MCITBA/Lok_Prak_Rob/Bilder/Gesamtsystem_hinten.png

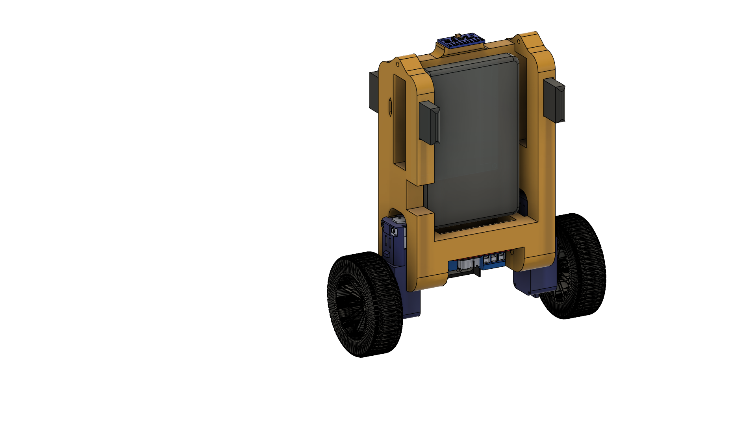
Bilder/Gesamtsystem_hinten.png
