MCITBA/Lok_Prak_Rob/iCloud Fotos/IMG_4470.PNG

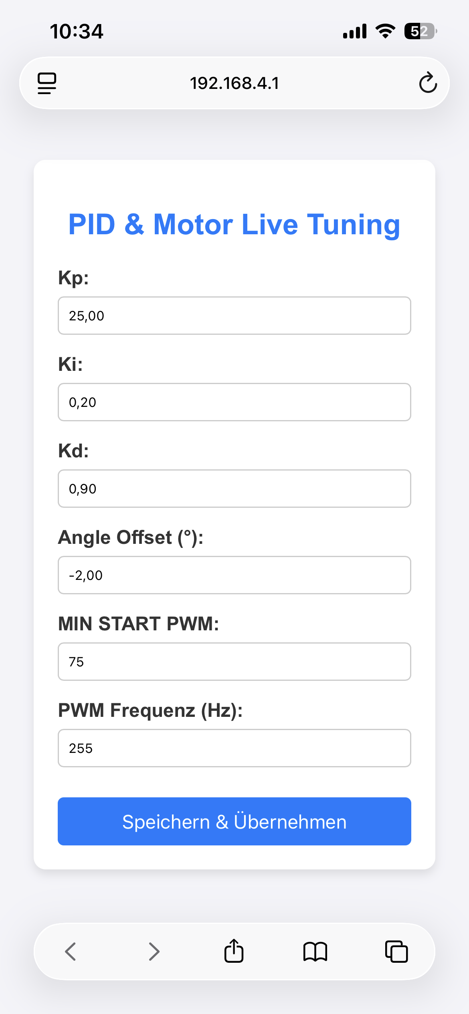
iCloud Fotos/IMG_4470.PNG
