MCITBA/Lok_Prak_Rob/iCloud Fotos/IMG_4471.PNG

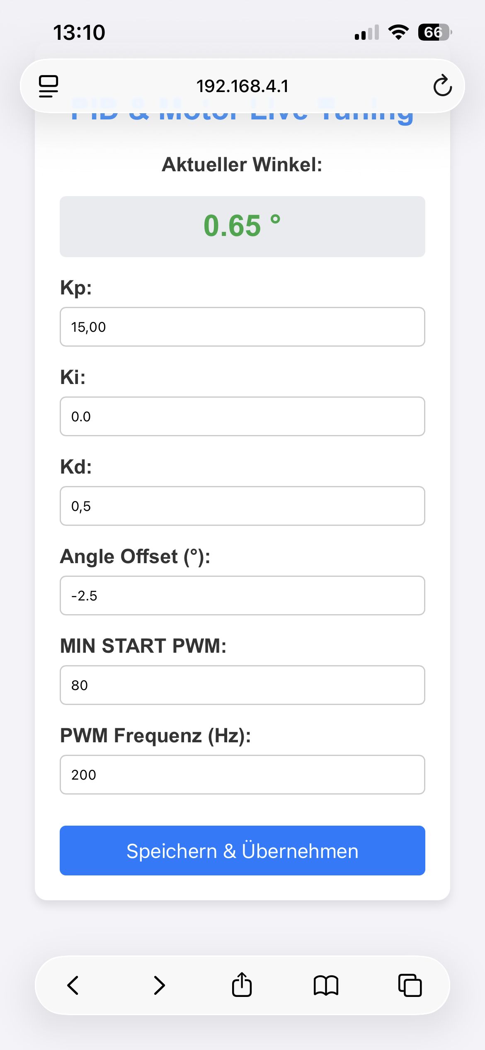
iCloud Fotos/IMG_4471.PNG
