MCITBA/Lok_Prak_Rob/iCloud Fotos/IMG_4481.JPEG

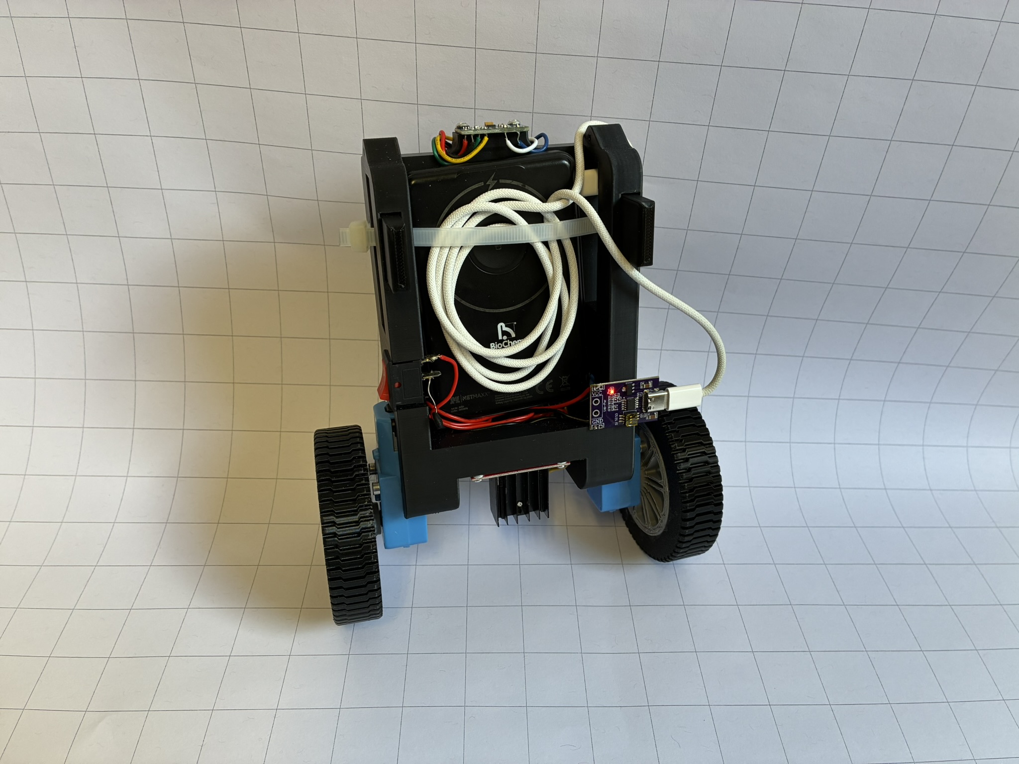
iCloud Fotos/IMG_4481.JPEG
