MCITBA/Lok_Prak_Rob/iCloud Fotos/IMG_4482.JPEG

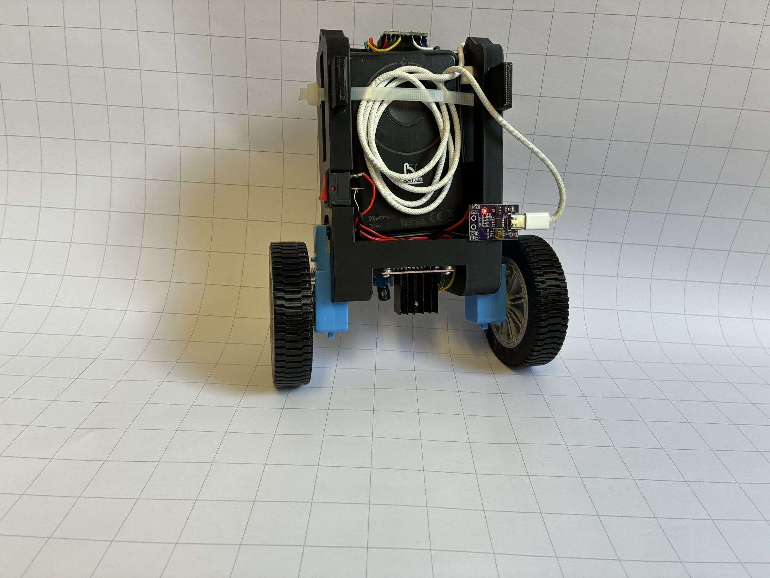
iCloud Fotos/IMG_4482.JPEG
