MCITBA/Lok_Prak_Rob/iCloud Fotos/IMG_4483.JPEG

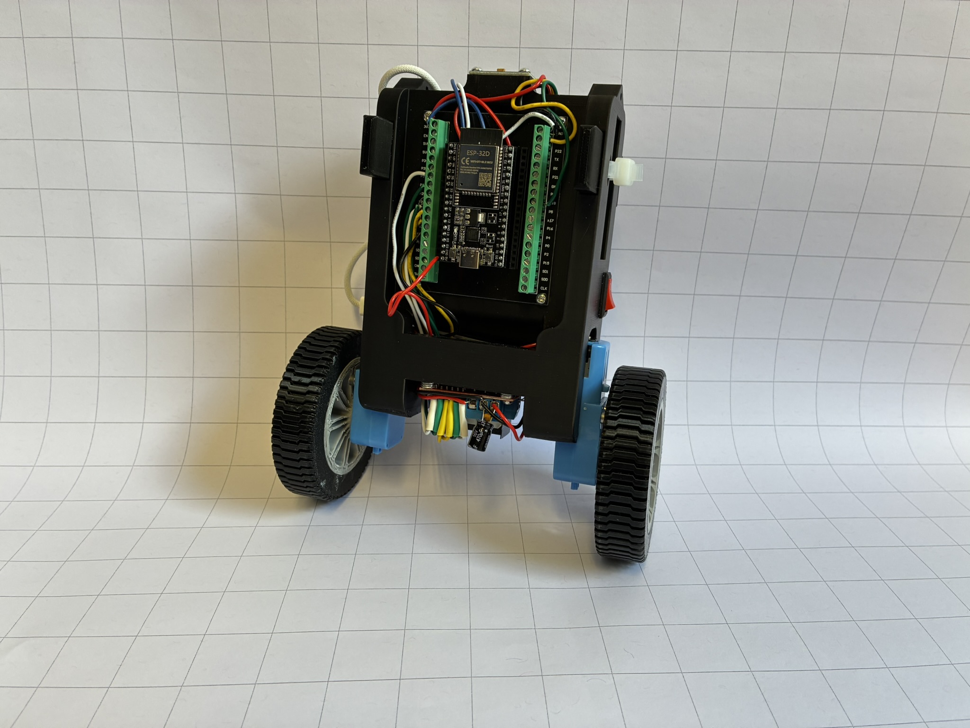
iCloud Fotos/IMG_4483.JPEG
